safaaraed99/COEN490/avr_firmware/avr_firmware/uart.c

/*
 * uart.c
 *
 * Created: 2024-03-16 2:15:14 PM
 *  Author: Matthew Faigan
 */ 

#include "uart.h"

#include <util/atomic.h>
#include <avr/interrupt.h>
#include <avr/io.h>

#include "circular_buffer.h"

// The clock rate of the system is 8 MHz.
// When not running the UART at double speed, UBRR = f_osc / (16*Baud) - 1
// The below value is for 9600 baud.
#define DEBUG_UBRR 51

// Circular buffers for debug/Bluetooth send and receive.
// When the main loop sends data, it's copied into the buffer.
// Data is asynchronously transmitted out of the buffer in the background using interrupts.
static volatile circular_buffer_t debug_send_buf;
static volatile circular_buffer_t debug_recv_buf;
//static volatile circular_buffer_t bt_send_buf;
//static volatile circular_buffer_t bt_recv_buf;

void setup_uart(void)
{
	// Initialize circular buffers for debug
	circ_buf_init(&debug_send_buf);
	circ_buf_init(&debug_recv_buf);
	//circ_buf_init(&bt_send_buf);
	//circ_buf_init(&bt_recv_buf);
	
	/* USART0 (Bluetooth) initialization */
	// Disabled for demo because UART0 not working properly
	//UCSR0B = (1<<RXCIE0) | (1<<UDRIE0) | (1<<RXEN0) | (1<<TXEN0);
	//UCSR0C = (1<UCSZ01) | (1<<UCSZ00);
	//UBRR0H = (unsigned char)(DEBUG_UBRR >> 8);
	//UBRR0L = (unsigned char)DEBUG_UBRR;
	
	/* USART1 (Debug serial) initialization */
	// Enable RX complete, TX data register empty interrupts. Enable receiver and transmitter.
	UCSR1B = (1<<RXCIE1) | (1<<UDRIE1) | (1<<RXEN1) | (1<<TXEN1);
	// Set asynchronous, no parity, 1 stop bit, 8 data bits.
	UCSR1C = (1<<UCSZ11) | (1<<UCSZ10);
	// Set baud rate.
	UBRR1H = (unsigned char)(DEBUG_UBRR >> 8);
	UBRR1L = (unsigned char)DEBUG_UBRR;
}

void debug_send(char* msg)
{
	ATOMIC_BLOCK(ATOMIC_RESTORESTATE)
	{
		circ_buf_write_str(&debug_send_buf, msg);
		// Enable the transmit data register empty interrupt
		UCSR1B |= (1<<UDRIE1);
	}
}

size_t debug_recv(char* dest, size_t dest_len)
{
	size_t bytes_read;
	ATOMIC_BLOCK(ATOMIC_RESTORESTATE)
	{
		bytes_read = circ_buf_read(&debug_recv_buf, dest, dest_len);
	}
	return bytes_read;
}

void bt_send_motor_warning(motor motor_num)
{
	char msg[2];
	msg[0] = 0xA1;
	msg[1] = motor_num;
	ATOMIC_BLOCK(ATOMIC_RESTORESTATE)
	{
		circ_buf_write_len(&debug_send_buf, msg, 2);
		UCSR1B |= (1<<UDRIE1);
	}
}

void bt_send_reading(potentiometer pot_num, int16_t reading)
{
	char msg[4];
	msg[0] = 0x81;
	msg[1] = pot_num;
	msg[2] = (char)(reading >> 8);
	msg[3] = (char)reading;
	ATOMIC_BLOCK(ATOMIC_RESTORESTATE)
	{
		circ_buf_write_len(&debug_send_buf, msg, 4);
		UCSR1B |= (1<<UDRIE1);
	}
}

// Fires when transmit data register is empty, indicating we can pump in the next byte
ISR(USART1_UDRE_vect)
{
	ATOMIC_BLOCK(ATOMIC_RESTORESTATE)
	{
		// Check if there's a byte to send; if there is then copy it into the data register
		char temp;
		size_t bytes_read = circ_buf_read(&debug_send_buf, &temp, 1);
		if (bytes_read == 1)
		{
			UDR1 = temp;
		}
		
		// Disable this interrupt if there's no more data in the buffer, otherwise this ISR will keep getting called forever
		if (circ_buf_get_len(&debug_send_buf) == 0)
		{
			UCSR1B &= ~(1<<UDRIE1);
		}
	}	
}

// Fires when the receive data register is full, indicating we can read in an incoming byte
ISR(USART1_RX_vect)
{
	ATOMIC_BLOCK(ATOMIC_RESTORESTATE)
	{
		// Copy the incoming byte out of the data register
		char temp;
		temp = UDR1;
		
		// Write the incoming byte into the receive buffer
		circ_buf_write_len(&debug_recv_buf, &temp, 1);
	}
}

//ISR(USART0_UDRE_vect)
//{
	//ATOMIC_BLOCK(ATOMIC_RESTORESTATE)
	//{
		//// Check if there's a byte to send; if there is then copy it into the data register
		//char temp;
		//size_t bytes_read = circ_buf_read(&bt_send_buf, &temp, 1);
		//if (bytes_read == 1)
		//{
			//UDR0 = temp;
		//}
		//
		//// Disable this interrupt if there's no more data in the buffer, otherwise this ISR will keep getting called forever
		//if (circ_buf_get_len(&bt_send_buf) == 0)
		//{
			//UCSR0B &= ~(1<<UDRIE0);
		//}
	//}
//}
//
//// Fires when the receive data register is full, indicating we can read in an incoming byte
//ISR(USART0_RX_vect)
//{
	//ATOMIC_BLOCK(ATOMIC_RESTORESTATE)
	//{
		//// Copy the incoming byte out of the data register into a null terminated string
		//char temp[2] = {0, 0};
		//temp[0] = UDR0;
		//
		//// Write the incoming byte into the receive buffer
		//circ_buf_write(&bt_recv_buf, temp);
	//}
//}
